aircitizen/aircitizen/hardware/plaque-souple/IMG_20190515_170904.jpg

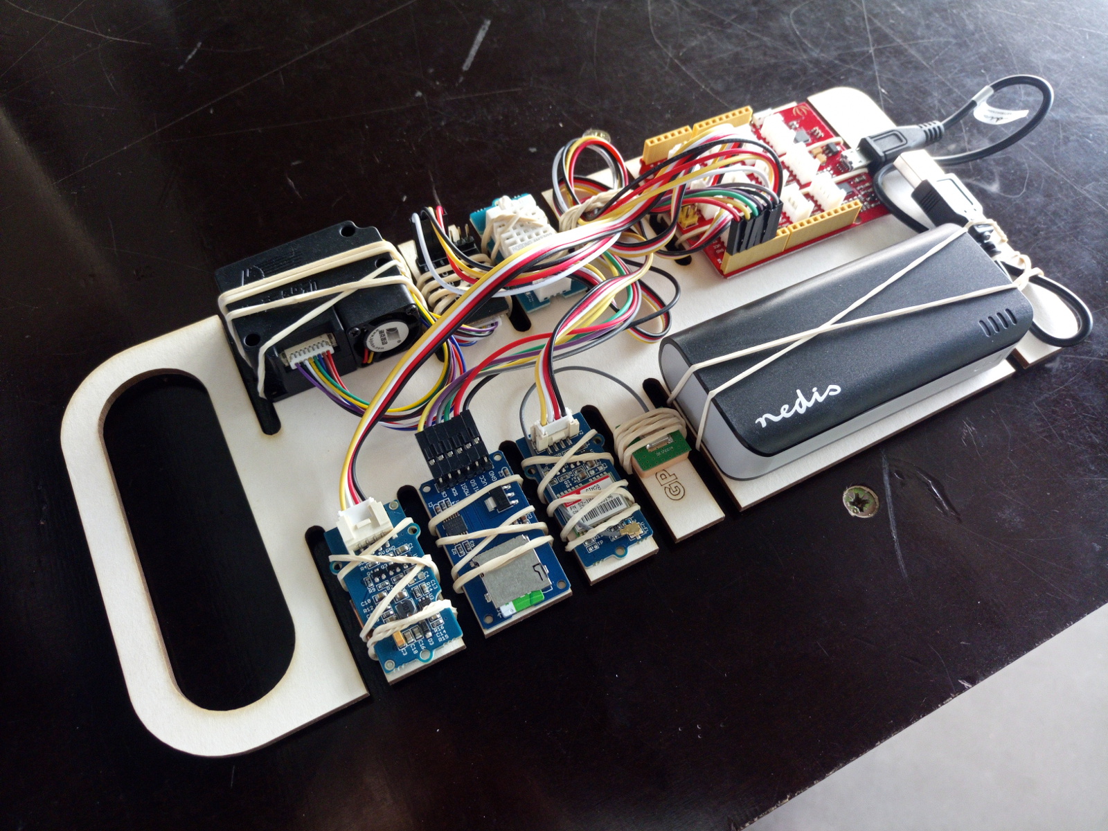
hardware/plaque-souple/IMG_20190515_170904.jpg
