aircitizen/aircitizen/hardware/plaque-souple/IMG_20190515_201537.jpg

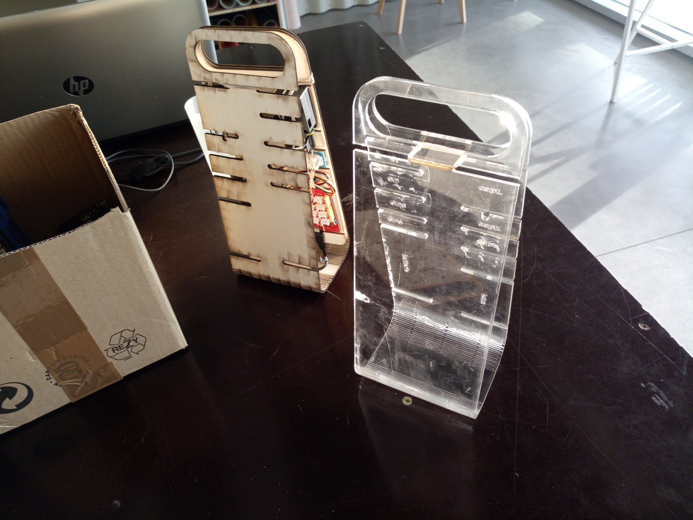
hardware/plaque-souple/IMG_20190515_201537.jpg
