aircitizen/aircitizen/hardware/plaque-souple/IMG_20190516_150140.jpg

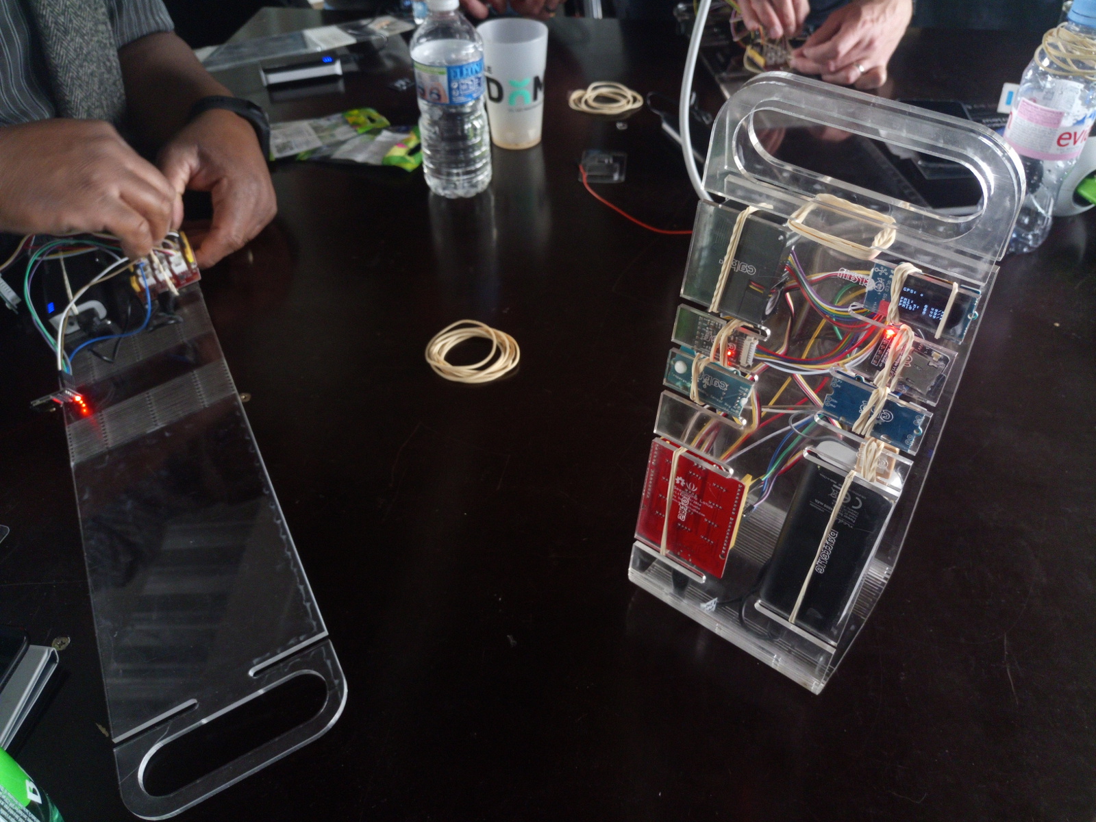
hardware/plaque-souple/IMG_20190516_150140.jpg
