aircitizen/aircitizen/hardware/turfu-prototype/IMG_20180927_105035.jpg

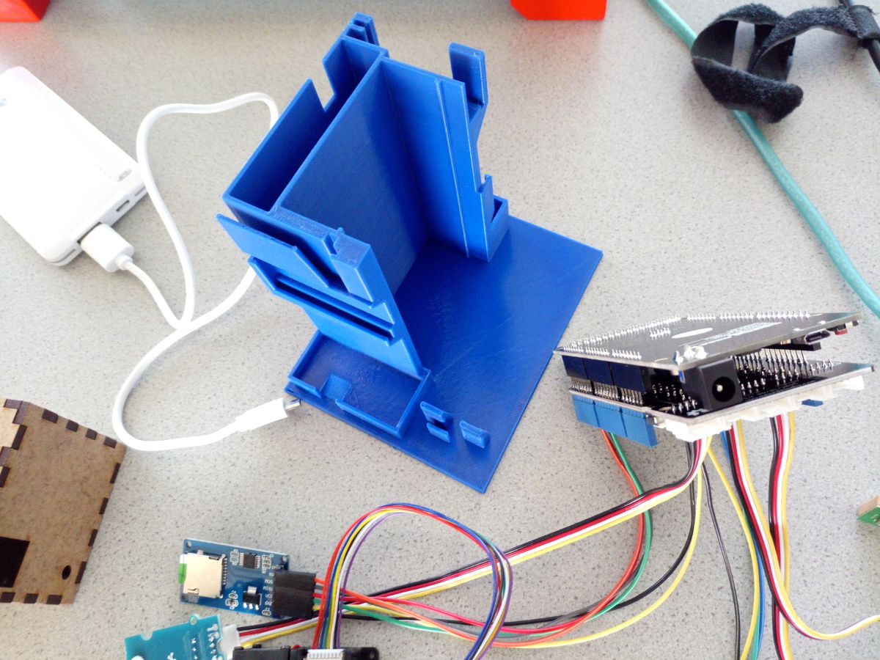
hardware/turfu-prototype/IMG_20180927_105035.jpg
