aircitizen/aircitizen/hardware/turfu-prototype/IMG_20180927_110015.jpg

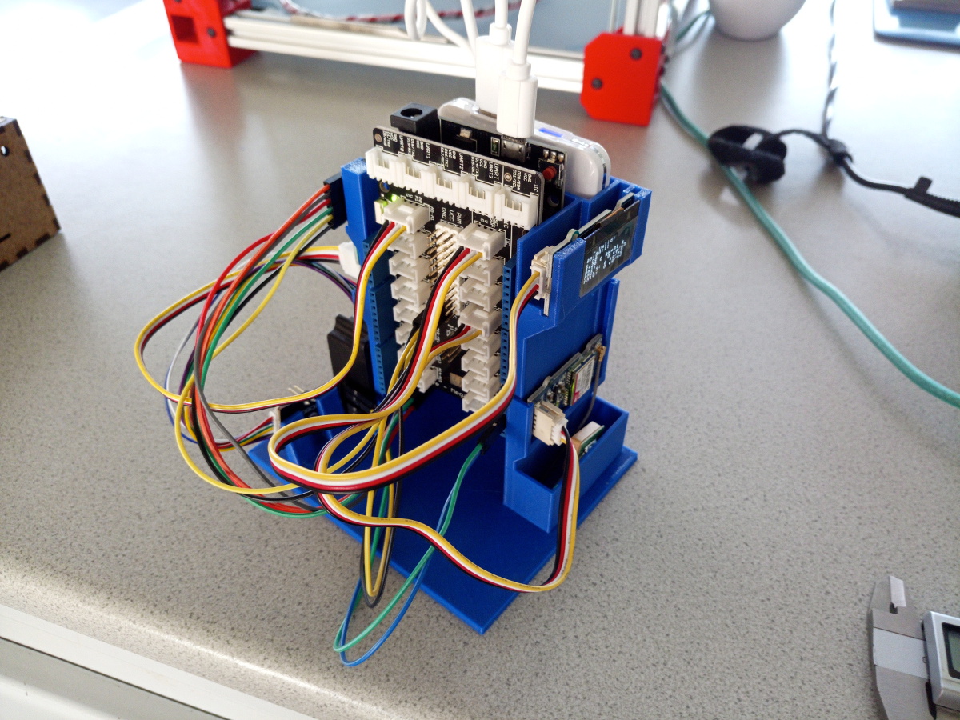
hardware/turfu-prototype/IMG_20180927_110015.jpg
