aircitizen/aircitizen/hardware/turfu-prototype/IMG_20180927_110024.jpg

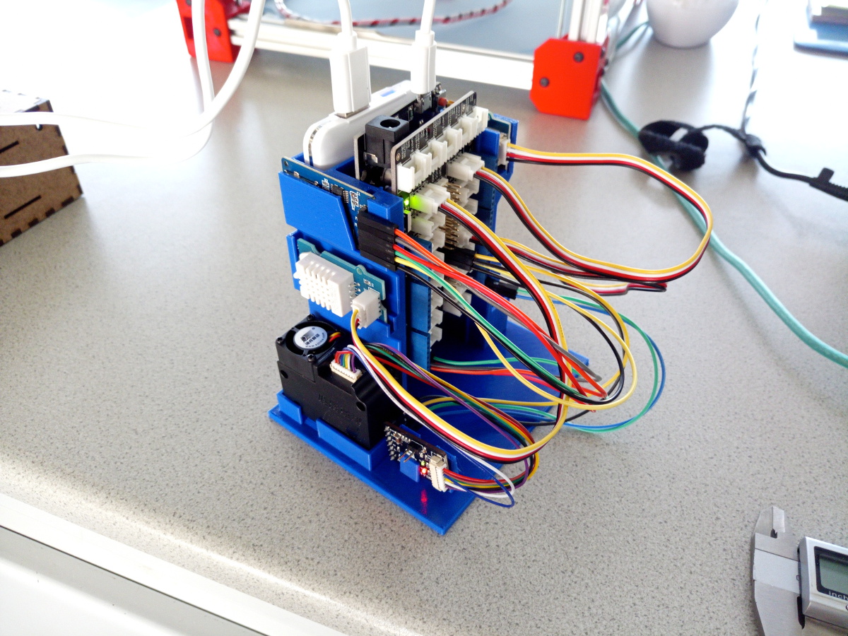
hardware/turfu-prototype/IMG_20180927_110024.jpg
