aircitizen/aircitizen/software/CN2-workshops/test_OLED-display/test_OLED-display.ino

/*

  PrintTest.pde
  
  How to use the base class "Print"
  
  >>> Before compiling: Please remove comment from the constructor of the 
  >>> connected graphics display (see below).
  
  Universal 8bit Graphics Library, https://github.com/olikraus/u8glib/
  
  Copyright (c) 2012, olikraus@gmail.com
  All rights reserved.

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
  THIS SOFTWARE IS PROVIDED BY THE COPYRIGHT HOLDERS AND 
  CONTRIBUTORS "AS IS" AND ANY EXPRESS OR IMPLIED WARRANTIES, 
  INCLUDING, BUT NOT LIMITED TO, THE IMPLIED WARRANTIES OF 
  MERCHANTABILITY AND FITNESS FOR A PARTICULAR PURPOSE ARE 
  DISCLAIMED. IN NO EVENT SHALL THE COPYRIGHT HOLDER OR 
  CONTRIBUTORS BE LIABLE FOR ANY DIRECT, INDIRECT, INCIDENTAL, 
  SPECIAL, EXEMPLARY, OR CONSEQUENTIAL DAMAGES (INCLUDING, BUT 
  NOT LIMITED TO, PROCUREMENT OF SUBSTITUTE GOODS OR SERVICES; 
  LOSS OF USE, DATA, OR PROFITS; OR BUSINESS INTERRUPTION) HOWEVER 
  CAUSED AND ON ANY THEORY OF LIABILITY, WHETHER IN CONTRACT, 
  STRICT LIABILITY, OR TORT (INCLUDING NEGLIGENCE OR OTHERWISE) 
  ARISING IN ANY WAY OUT OF THE USE OF THIS SOFTWARE, EVEN IF 
  ADVISED OF THE POSSIBILITY OF SUCH DAMAGE.  
  
*/


#include "U8glib.h"

U8GLIB_SSD1306_128X32 u8g(U8G_I2C_OPT_NONE);	// I2C / TWI 

void draw(void) {
  // graphic commands to redraw the complete screen should be placed here  
  u8g.setFont(u8g_font_unifont);
  u8g.setPrintPos(0, 20); 
  // call procedure from base class, http://arduino.cc/en/Serial/Print
  u8g.print("Hello World!");
}

void setup(void) {
  // flip screen, if required
  // u8g.setRot180();
}

void loop(void) {
  // picture loop
  u8g.firstPage();  
  do {
    draw();
  } while( u8g.nextPage() );
  
  // rebuild the picture after some delay
  delay(500);
}
